fablabppdelectronica/PPDuinoNano/files/img/1.png

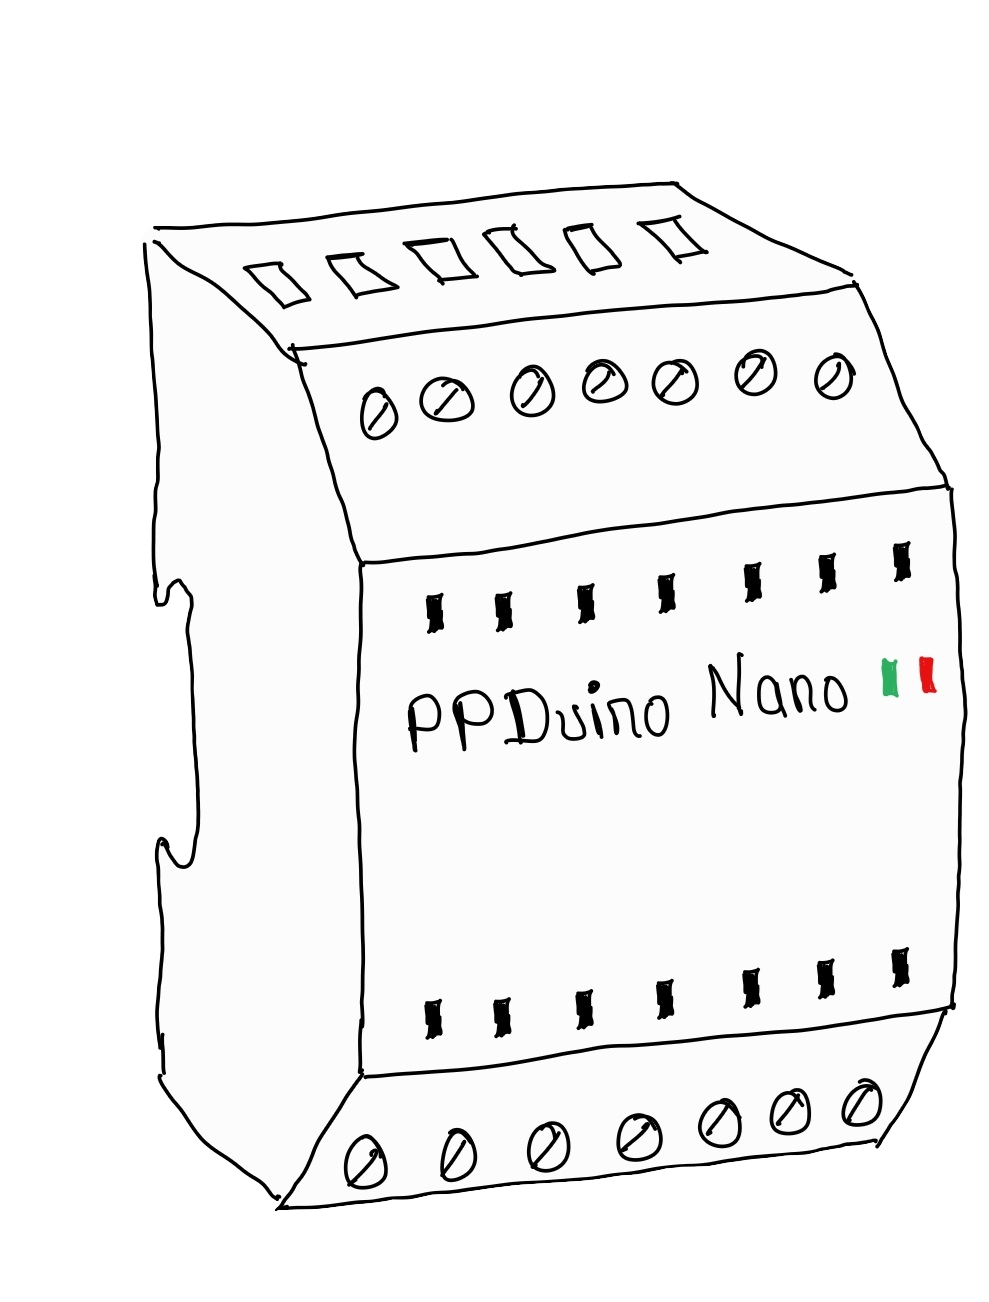
files/img/1.png
