fablabppdelectronica/PPDuinoNano/files/img/2.png

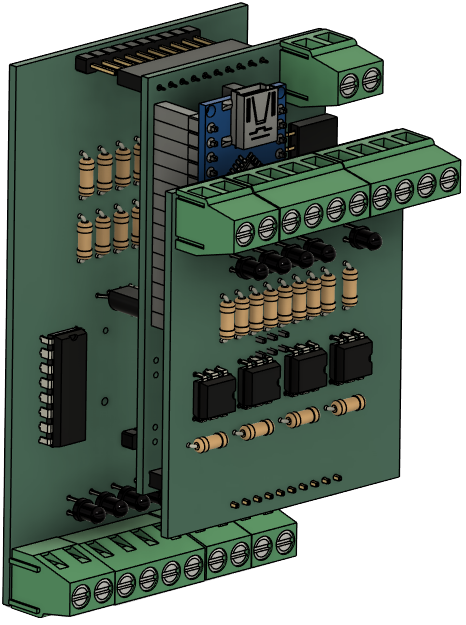
files/img/2.png
