fablabppdelectronica/PPDuinoNano/files/img/3.png

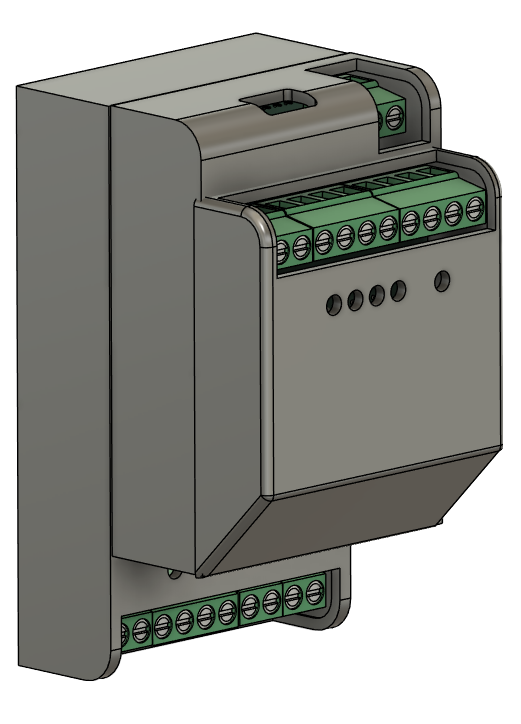
files/img/3.png
