fablabppdelectronica/PPDuinoNano/PPDuino_Nano_CPU/PCB_Electronic/V0.1/Salidas/PPDuino Nano Salidas COMP.pdf

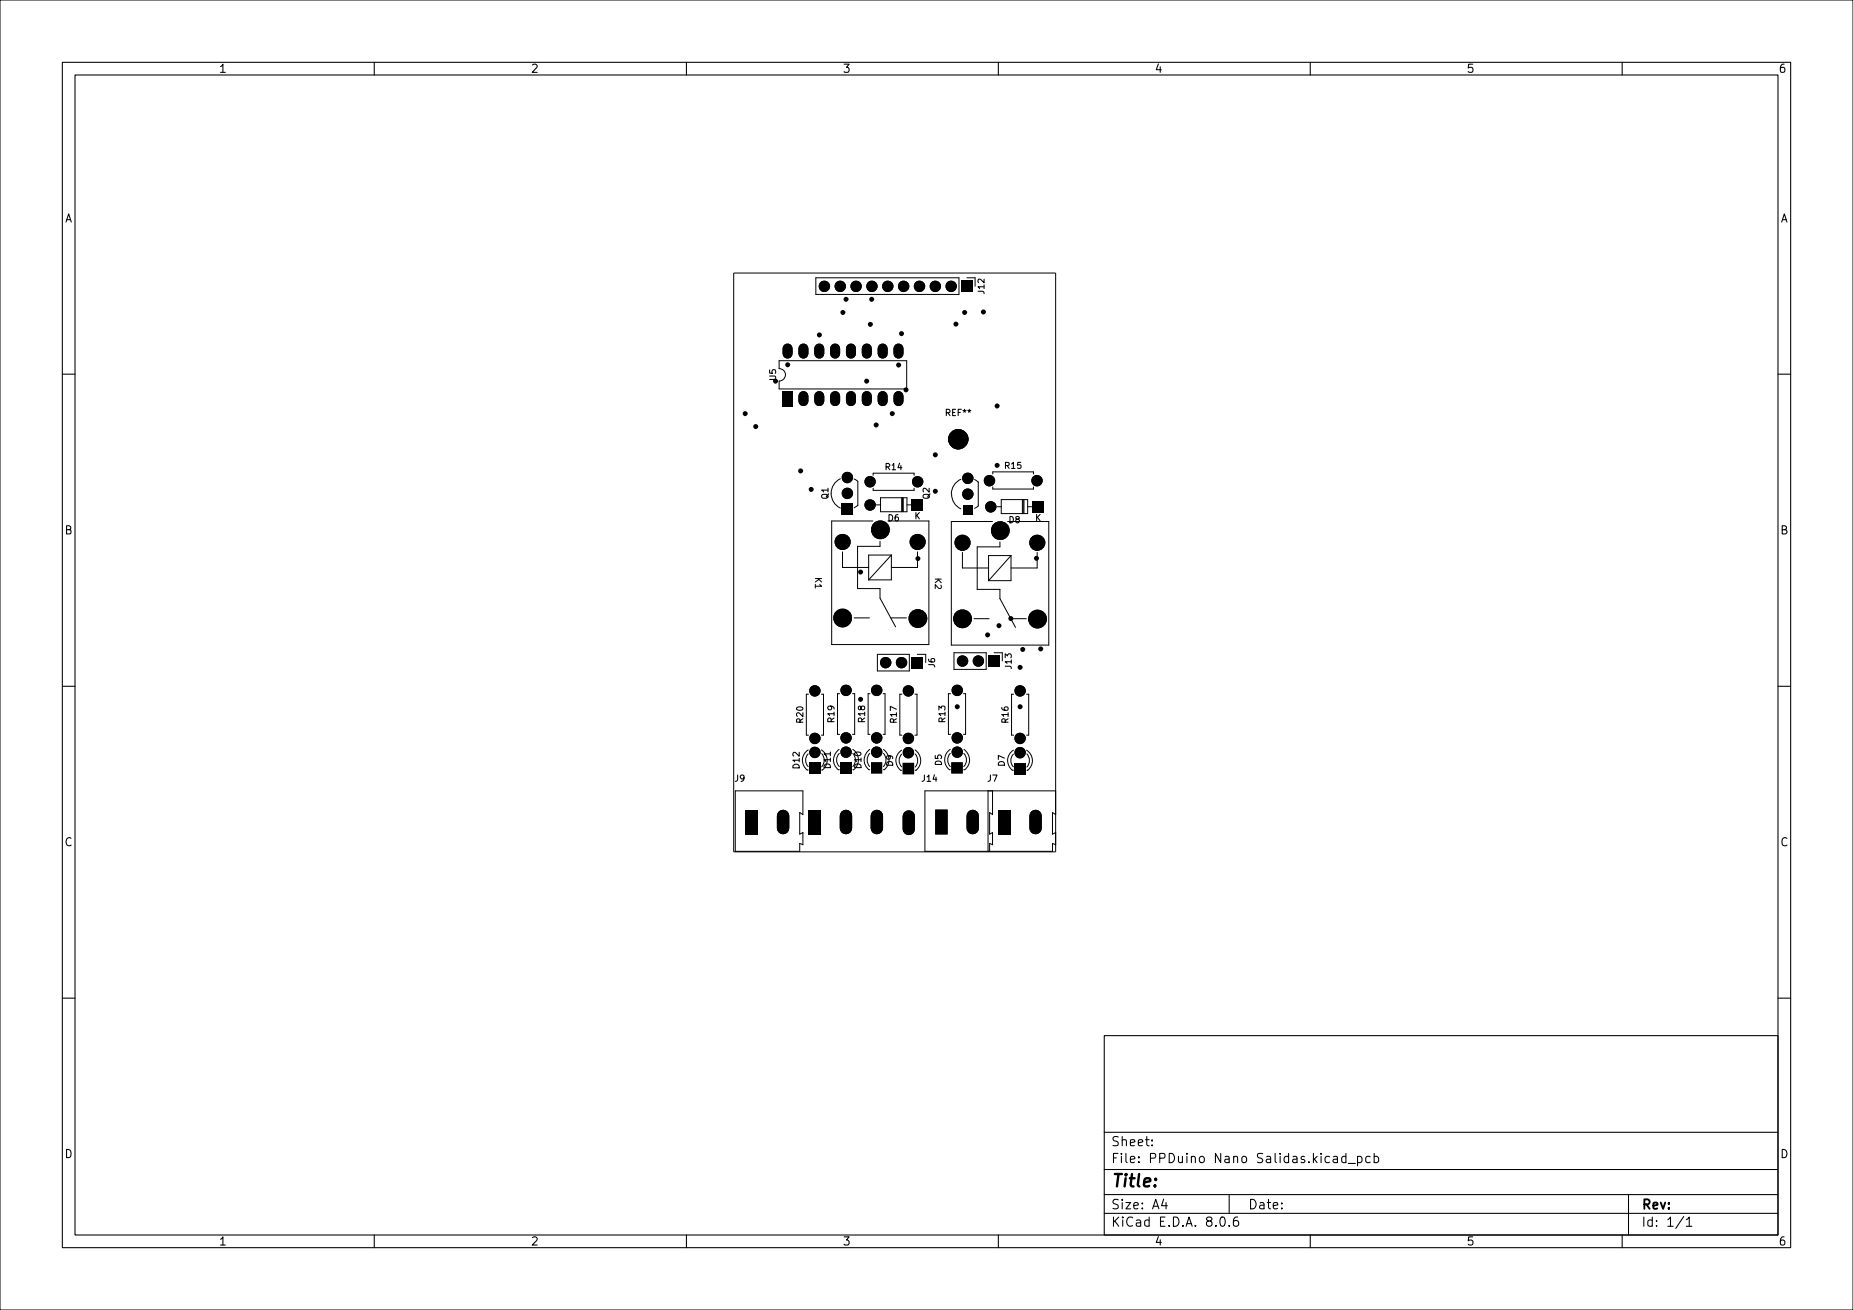
[picture p48: page 1]
