fablabppdelectronica/PPDuinoNano/PPDuino_Nano_CPU/PCB_Electronic/V0.1/Salidas/PPDuino Nano Salidas PCB Color.pdf

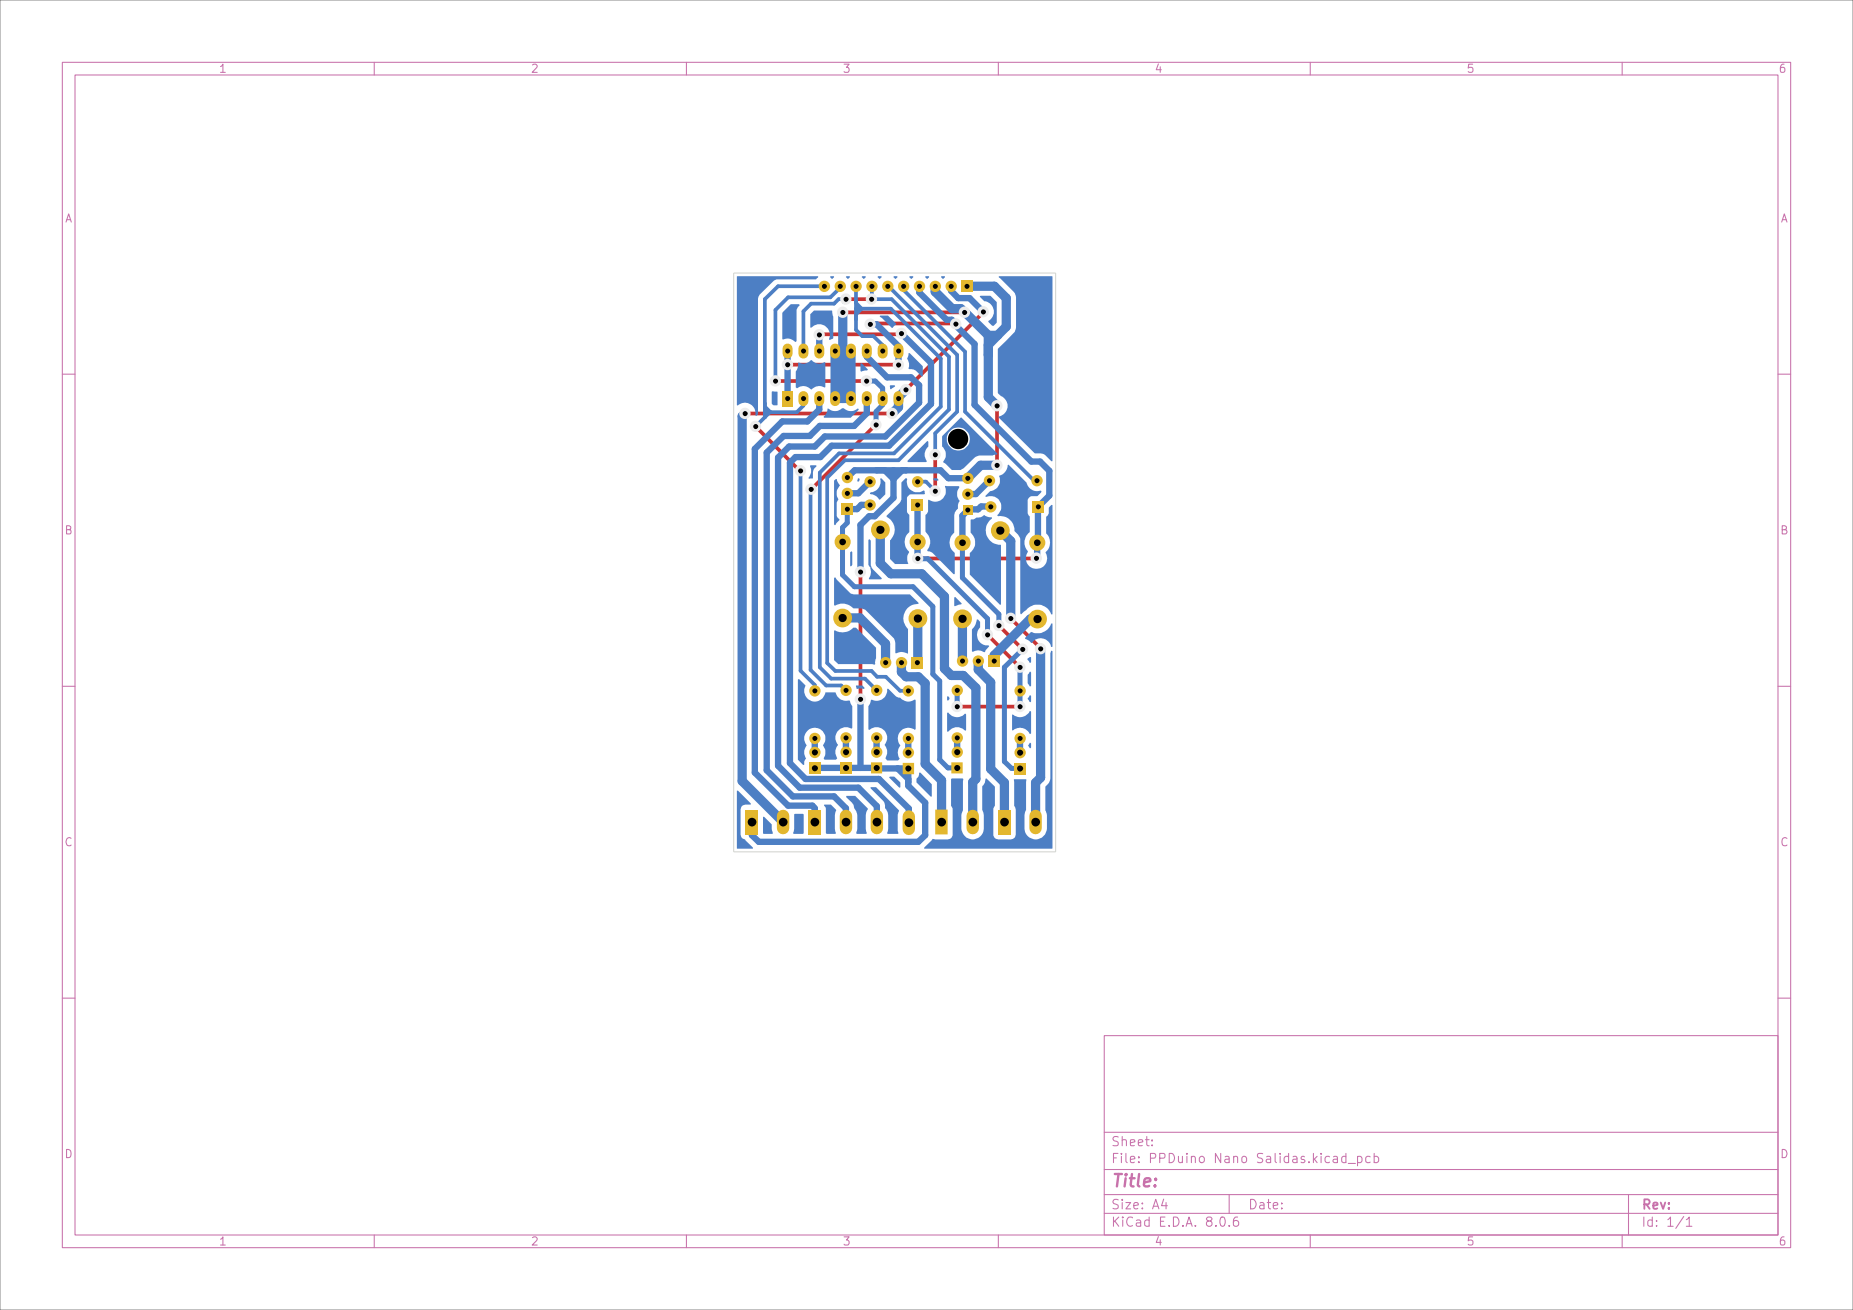
[picture p49: page 1]
