fablabppdelectronica/PPDuinoNano/PPDuino_Nano_CPU/PCB_Electronic/V0.1/Salidas/PPDuino Nano Salidas SCH.pdf

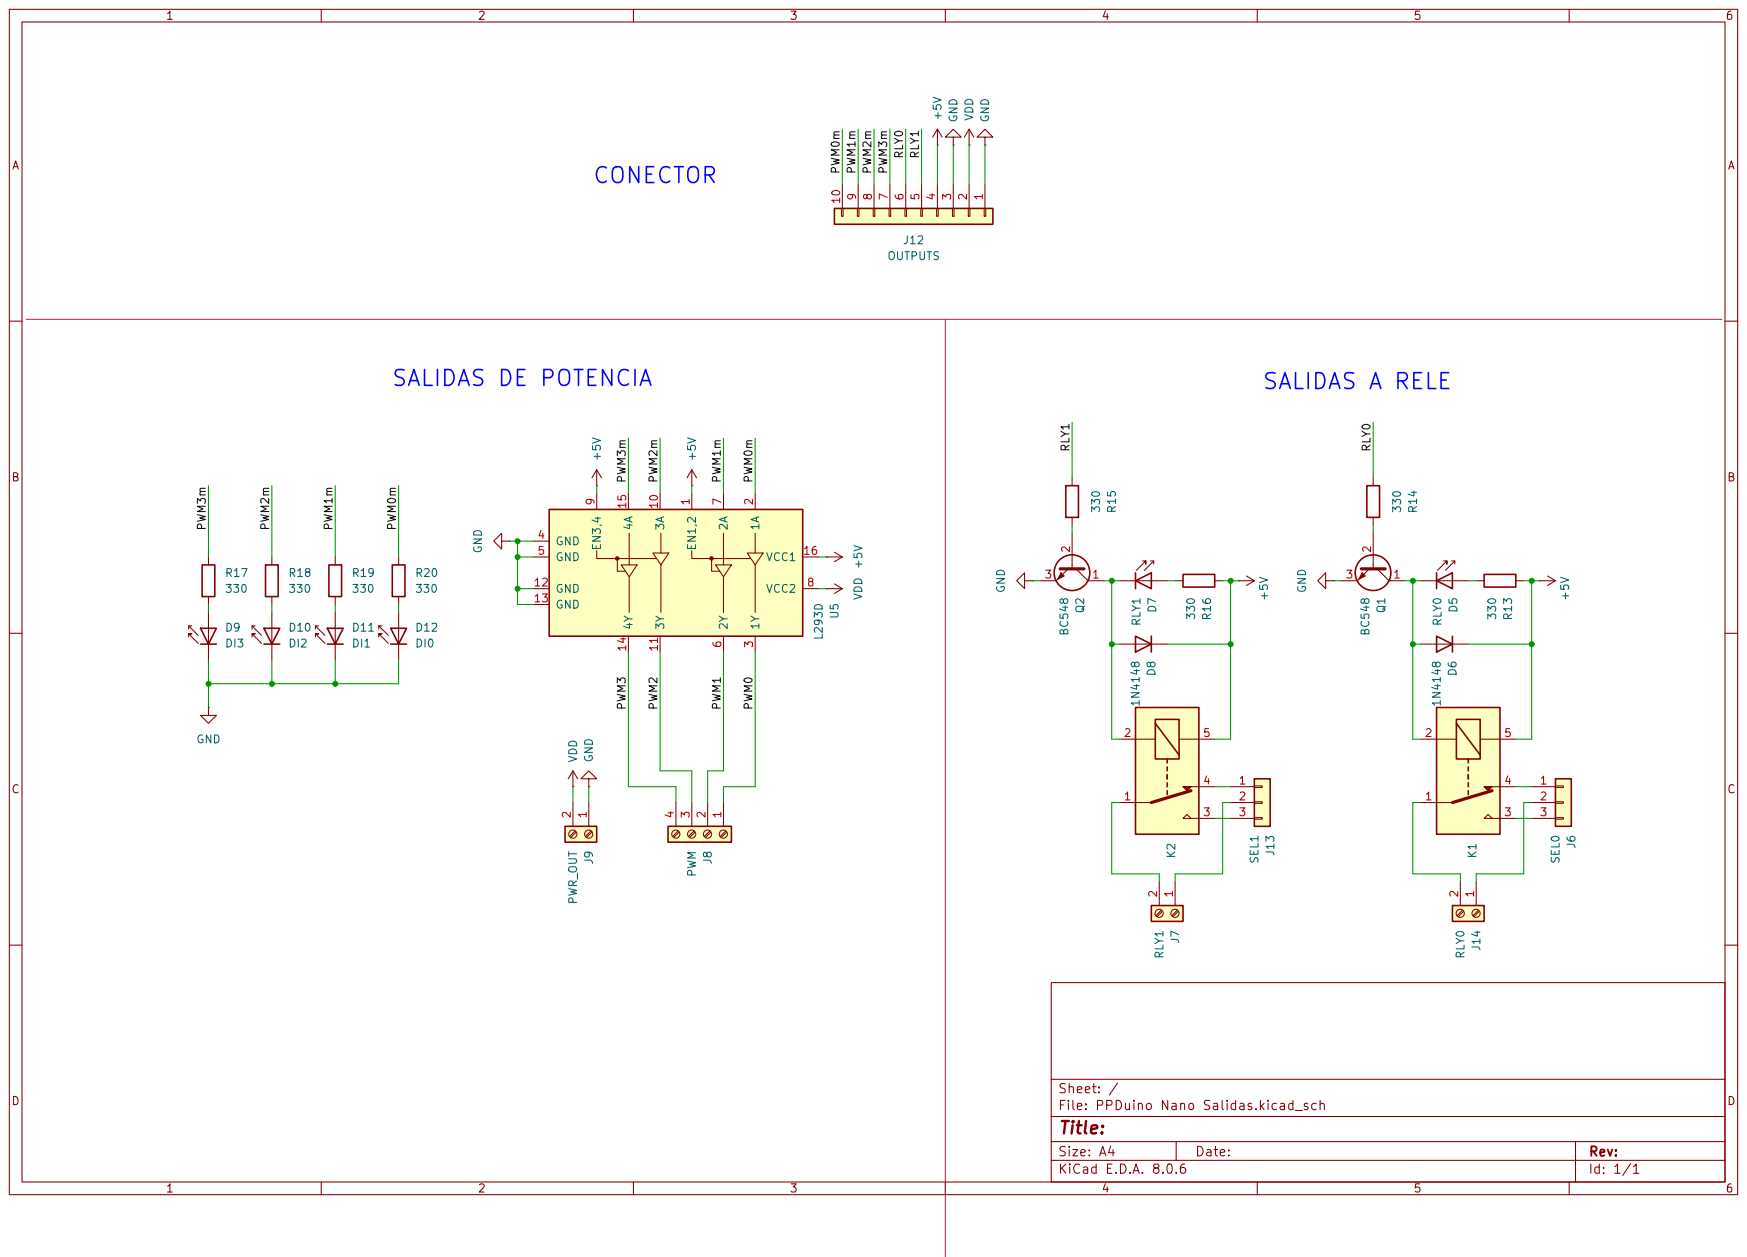
[picture p50: page 1]
